NilbinSec/DC34_Main_Badge_Fuzzer_SAO/DCBadgeFuzzer.kicad_sch

## KiCad design DCBadgeFuzzer.kicad_sch (2026-06-02)

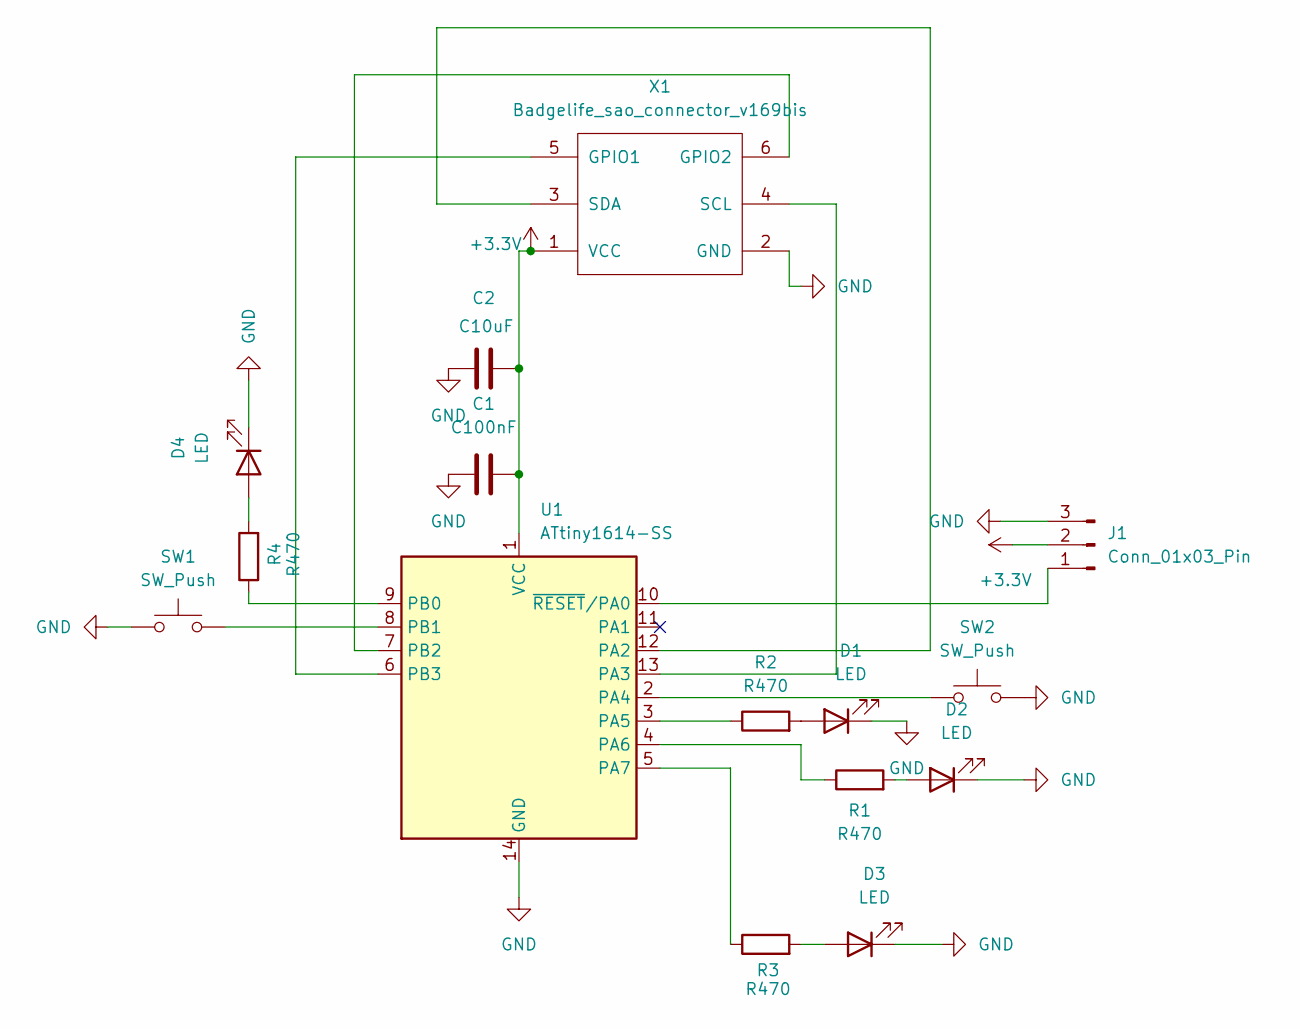
[picture p2: schematic DCBadgeFuzzer.kicad_sch]

Parts:
C1: C100nF; C_0805_2012Metric_Pad1.18x1.45mm_HandSolder
C2: C10uF; C_0805_2012Metric_Pad1.18x1.45mm_HandSolder
D1, D2, D3, D4: LED; LED_1206_3216Metric_Pad1.42x1.75mm_HandSolder
J1: Conn_01x03_Pin; PinSocket_1x03_P2.54mm_Vertical
R1, R2, R3, R4: R470; R_0805_2012Metric_Pad1.20x1.40mm_HandSolder
SW1, SW2: SW_Push; SW_TS04-66-85-BK-160-SMT
U1: ATtiny1614-SS; SOIC-14_3.9x8.7mm_P1.27mm
X1: Badgelife_sao_connector_v169bis; Badgelife-SAOv169-SAO-2x3

Connections:
+3.3V: C1.1, C2.1, J1.2, U1.1 (VCC), X1.1 (VCC)
GND: C1.2, C2.2, D1.1 (K), D2.1 (K), D3.1 (K), D4.1 (K), J1.3, SW1.1, SW2.2, U1.14 (GND), X1.2 (GND)
unnamed: D1.2 (A), R2.2
unnamed: D2.2 (A), R1.2
unnamed: D3.2 (A), R3.2
unnamed: D4.2 (A), R4.2
unnamed: J1.1, U1.10 (~RESET/PA0)
unnamed: R1.1, U1.4 (PA6)
unnamed: R2.1, U1.3 (PA5)
unnamed: R3.1, U1.5 (PA7)
unnamed: R4.1, U1.9 (PB0)
unnamed: SW1.2, U1.8 (PB1)
unnamed: SW2.1, U1.2 (PA4)
unnamed: U1.6 (PB3), X1.5 (GPIO1)
unnamed: U1.7 (PB2), X1.6 (GPIO2)
unnamed: U1.12 (PA2), X1.3 (SDA)
unnamed: U1.13 (PA3), X1.4 (SCL)
